mikeenting/RC-lap-timer/img/IMG_1789.jpeg

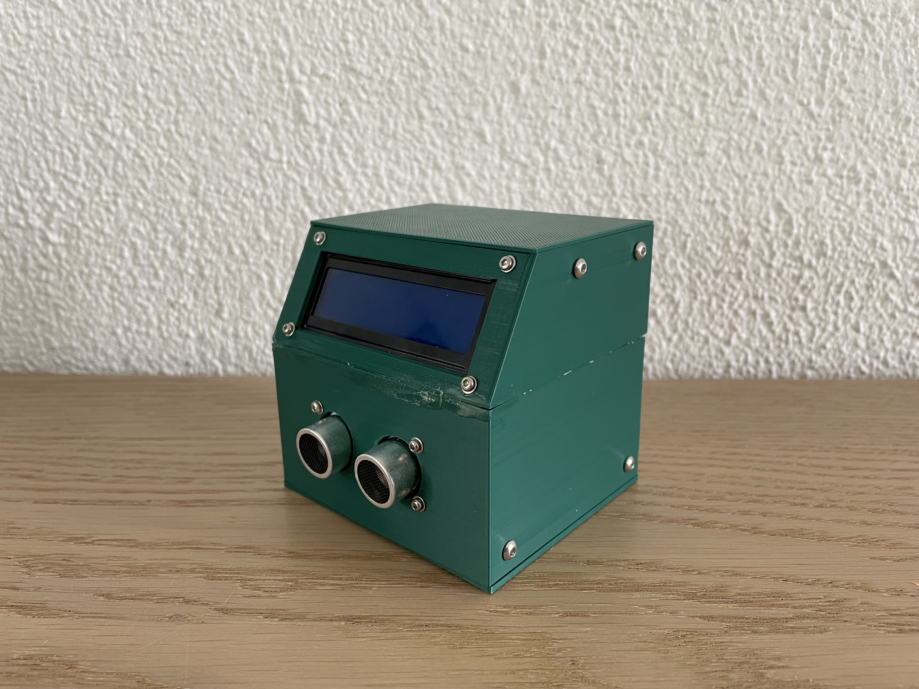
img/IMG_1789.jpeg
