mikeenting/RC-lap-timer/img/IMG_1790.jpeg

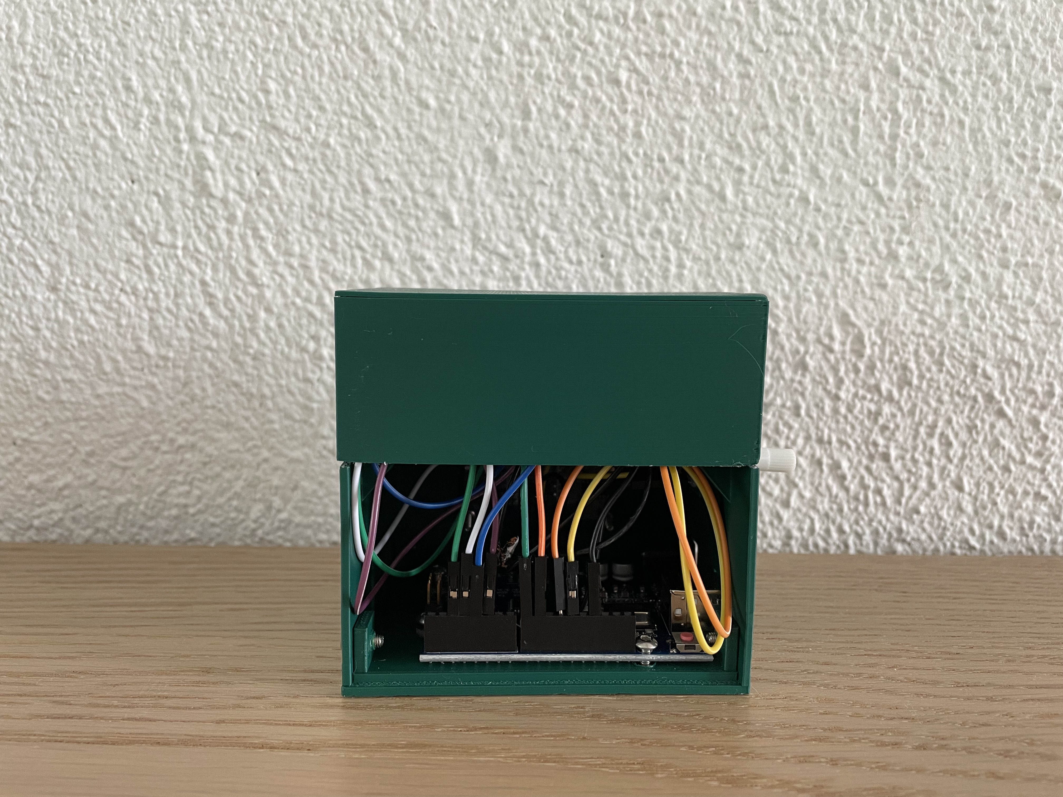
img/IMG_1790.jpeg
