mikeenting/RC-lap-timer/img/IMG_1791.jpeg

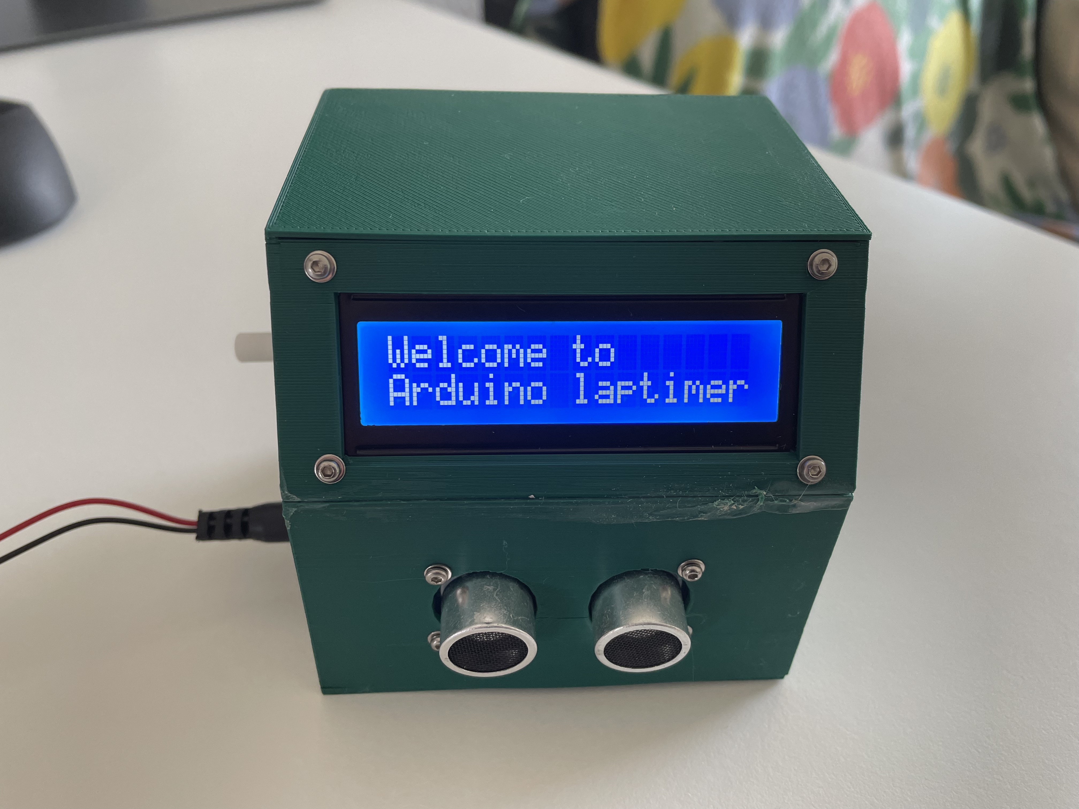
img/IMG_1791.jpeg
